sergeyfk05/AudioSwitcherSTM/AudioSwitcherNew/Channel.cpp

#include "Channel.h"
#include <stm32f10x.h>

namespace Models
{

	Channel::Channel(uint8_t ADCCh, GPIO_TypeDef* gPIOGroup, uint8_t pin, uint8_t ADCST, uint16_t MBL, uint32_t MF, uint8_t SC, GPIO_TypeDef* switcherGPIOGroup, uint8_t switcherPin)
		: ADCChannel(ADCCh)
		, Pin(pin)
		, GPIOGroup(gPIOGroup)
		, ADCSampleTime(ADCST)
		, MeasurementsBufferLength(MBL)
		, MeasurementFrequency(MF)
		, MeasurementsBuffer((uint8_t*)malloc(sizeof(uint8_t) * MBL))
		, SkipCoef(SC)
	{
		Switcher = new ChannelSwitcher(switcherGPIOGroup, switcherPin);
	}
	Channel::~Channel()
	{
		delete MeasurementsBuffer;
		delete Switcher;
	}

	//method which write value to buffer
	void Channel::WriteMeasurement(uint8_t value)
	{
		if (skipped < SkipCoef)
		{
			skipped++;
			return;
		}
	
		skipped = 1;
		MeasurementsBuffer[currentPos++] = value;
		currentPos %= MeasurementsBufferLength;
	}
	//get start position in buffer arrayy
	uint32_t Channel::GetCurrentPos()
	{
		return currentPos;
	}

	
	GPIO_TypeDef* Channel::GetGPIOGroup()
	{
		return GPIOGroup;
	}
	
	ChannelSwitcher* Channel::GetSwitcher()
	{
		return Switcher;
	}
	
}
